Malloc-Luo/CourseDesign/RemoteCtrlMod/inc/module.h

/******************************************************
 * @filename module.h
 * @brief 此模块中定义了一些全局使用的变量及宏定义
 *        此模块中定义了各模块的外部接口
 ******************************************************/
#ifndef __MODULE_H__
#define __MODULE_H__

typedef unsigned char uint8_t;
typedef unsigned int  uint16_t;
typedef unsigned long uint32_t;

typedef signed char int8_t;
typedef signed int  int16_t;
typedef signed long int32_t;

/* 最高温度设为100°C */
#define MAX_TEMP 1000

/**
 * 温控模块的温度
 * 将获取到的温度 * 10后转换成16位整形
 */
extern int16_t ModTemperture;

/*
 * 设定的温度值，在LCDdisplay.h中管理
 */
extern int16_t SetTemperture;

/*
 * 最低参考温度，温度设定值不能低于这个值
 */
extern int16_t RefTemperture;

/*
 * 下位机指令
 */
#define SET_VAL   0x01
#define ACTUL_VAL 0x02
#define RESET     0x04

extern uint8_t SlaveCmd;
/*
 * 任务函数
 */

// 10Hz
extern void Task_10Hz_1();
extern void Task_10Hz_2();

extern void Task_5Hz();
// 2Hz
extern void Task_2Hz();

#endif
