Malloc-Luo/CourseDesign/TempMeasureMod/inc/ADtemp.h

#ifndef __ADTEMP_H__
#define __ADTEMP_H__
#include "module.h"

/*
 * 获取当前温度值 0~999
 */
extern int16_t get_actulval(void);

/*
 * 制冷、制热
 * state = 0 制冷
 * state = 1 制热
 * state = 2 关闭设备，自由冷却
 */
#define COLD 0x00
#define HEAT 0x01
#define CLOSE 0x02
extern void ctrl_device(uint8_t state);

/*
 * CS5550初始化
 */
extern void CS5550Init();
extern uint32_t read_w(uint8_t cmd);


extern int32_t Temp1;
extern int32_t Temp2;
extern int32_t TempP;
extern bit isUpdataVal;


#endif
